jobinson99/EV-KuaFu/docs/images/mmexport1573315276697.jpg

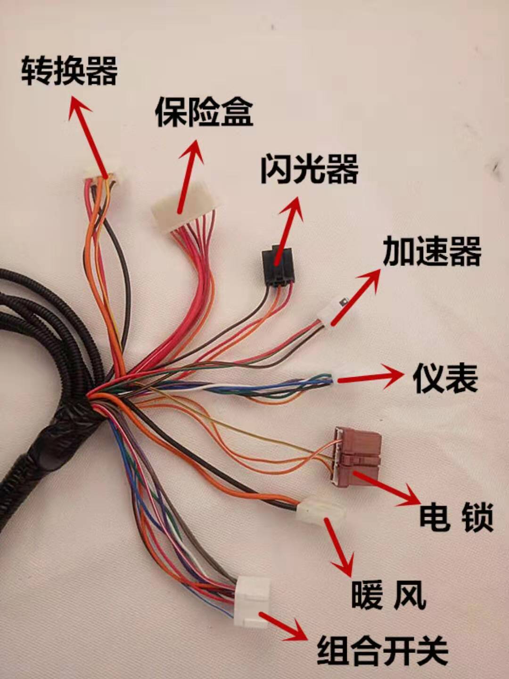
docs/images/mmexport1573315276697.jpg
