jobinson99/EV-KuaFu/docs/images/mmexport1573315287228.jpg

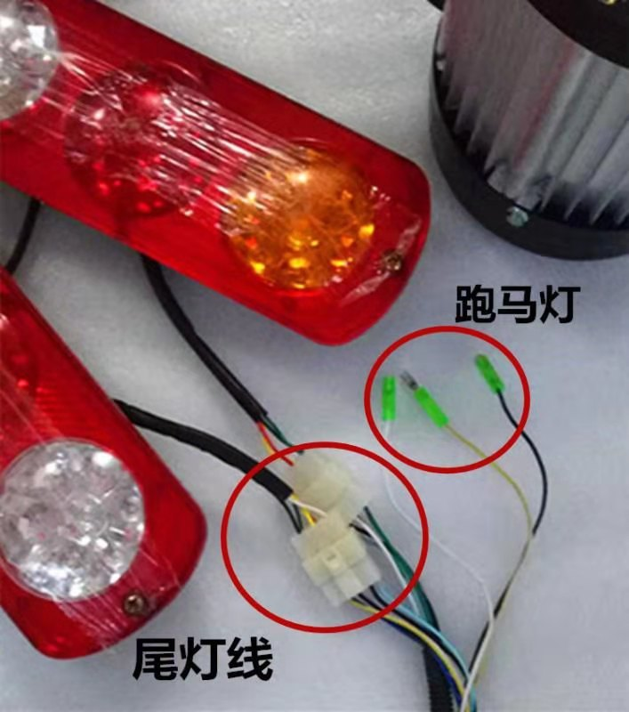
docs/images/mmexport1573315287228.jpg
