jobinson99/EV-KuaFu/docs/images/mmexport1573315331825.jpg

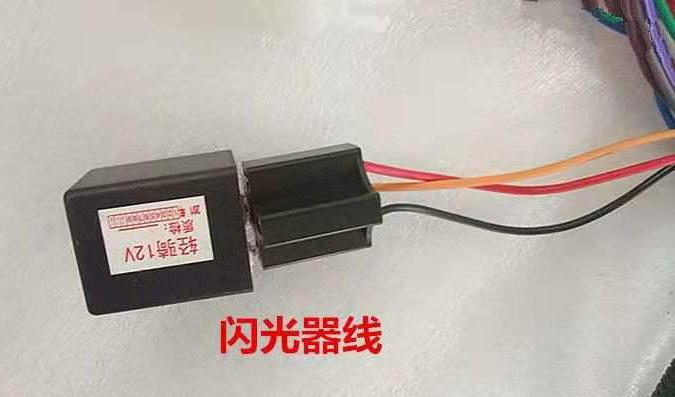
docs/images/mmexport1573315331825.jpg
