jobinson99/EV-KuaFu/docs/images/mmexport1573315335259.jpg

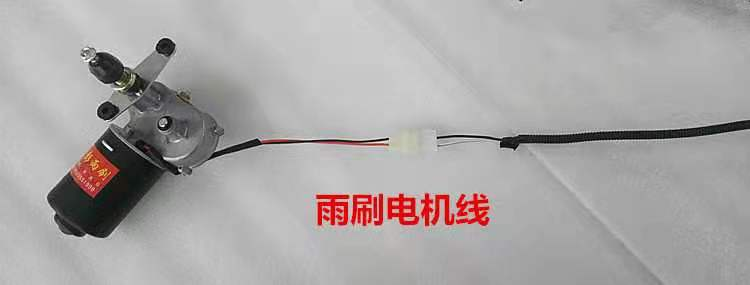
docs/images/mmexport1573315335259.jpg
