jobinson99/EV-KuaFu/docs/images/mmexport1573315338866.jpg

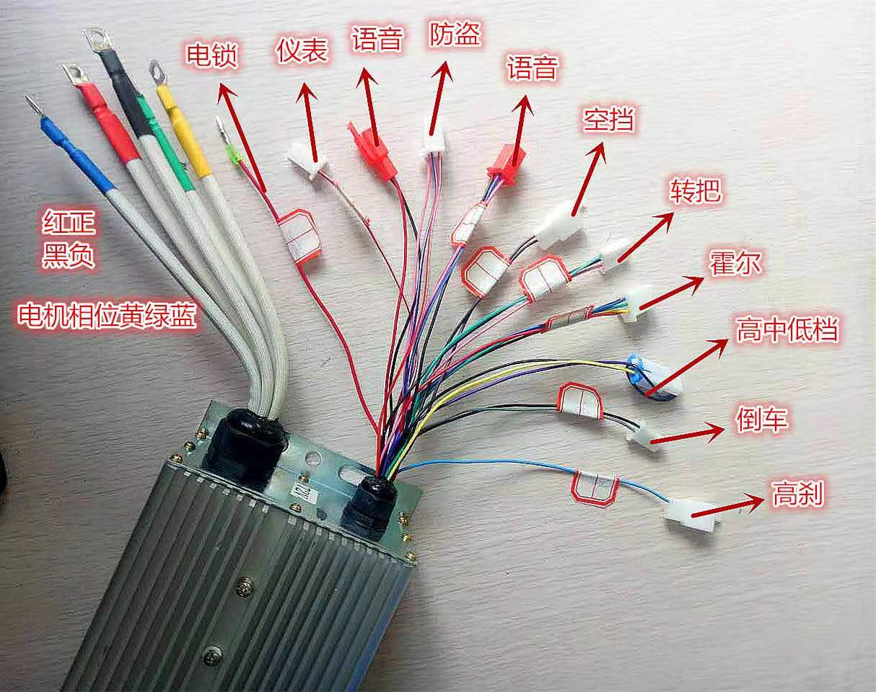
docs/images/mmexport1573315338866.jpg
