jobinson99/EV-KuaFu/docs/images/mmexport1573315342086.jpg

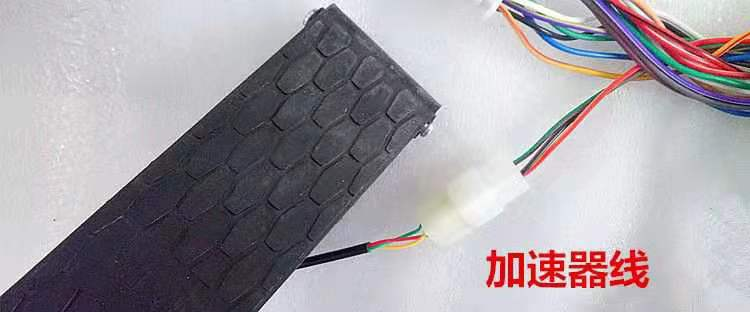
docs/images/mmexport1573315342086.jpg
