jobinson99/EV-KuaFu/docs/images/mmexport1573315346391.jpg

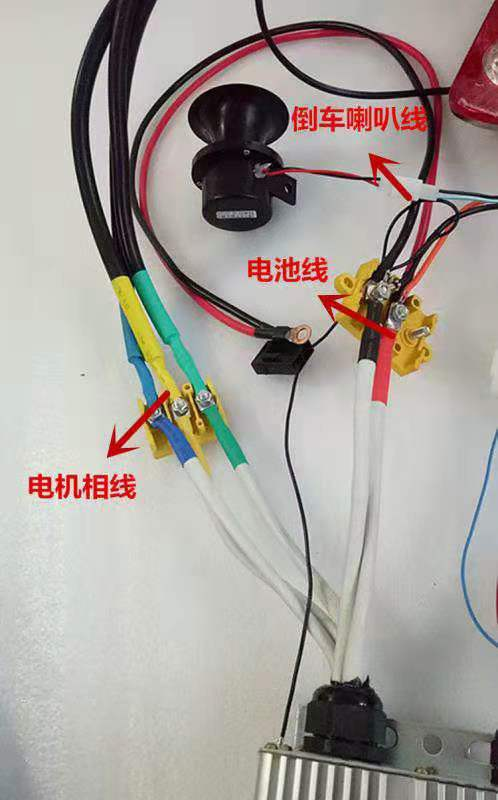
docs/images/mmexport1573315346391.jpg
