jobinson99/EV-KuaFu/docs/images/mmexport1573315385713.jpg

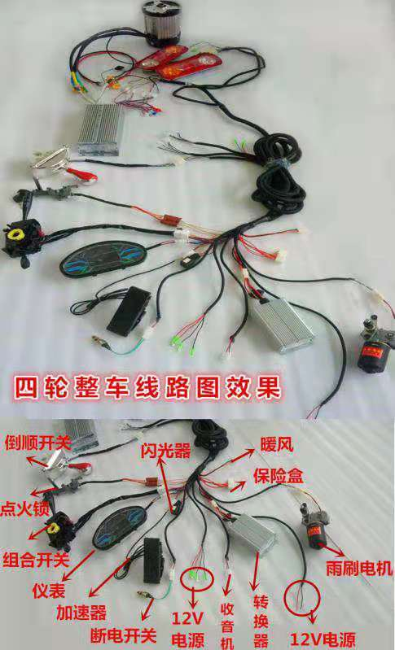
docs/images/mmexport1573315385713.jpg
