jobinson99/EV-KuaFu/docs/images/mmexport1573315388638.jpg

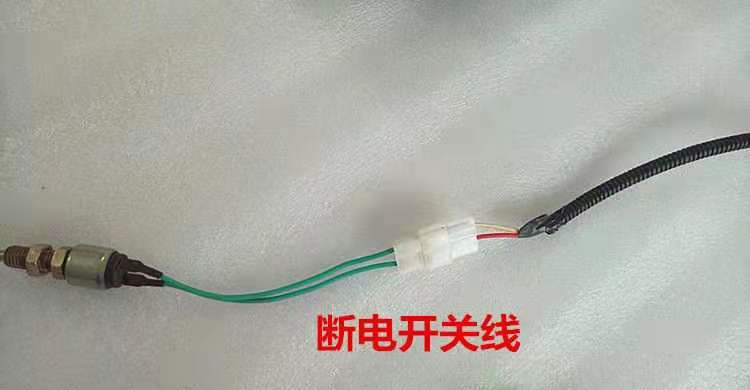
docs/images/mmexport1573315388638.jpg
