jobinson99/EV-KuaFu/docs/images/mmexport1573315394884.jpg

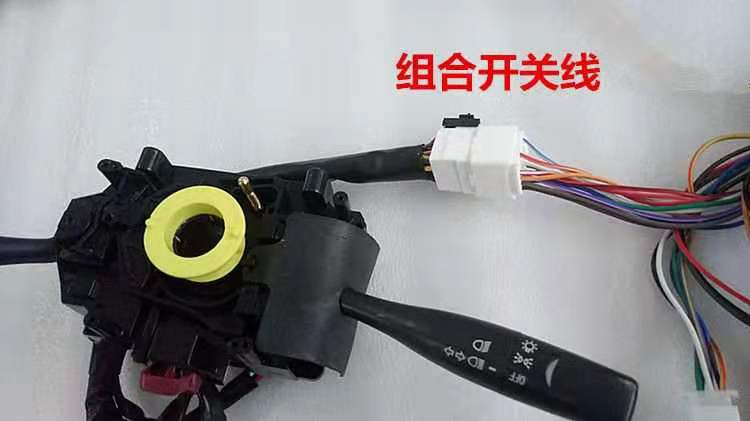
docs/images/mmexport1573315394884.jpg
