jobinson99/EV-KuaFu/docs/images/mmexport1574041762110.jpg

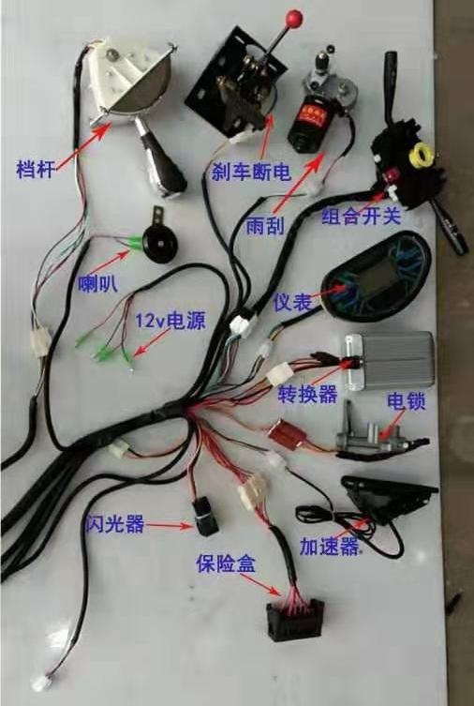
docs/images/mmexport1574041762110.jpg
