jobinson99/EV-KuaFu/docs/images/mmexport1574041777564.jpg

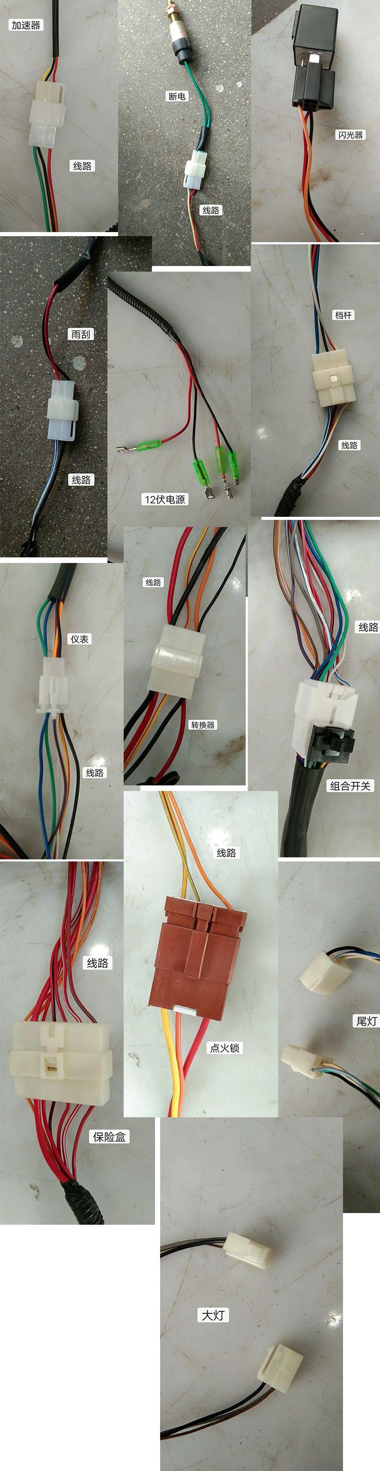
docs/images/mmexport1574041777564.jpg
