jobinson99/EV-KuaFu/docs/images/mmexport1574041887798.jpg

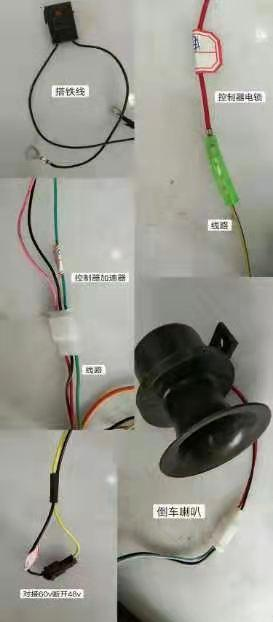
docs/images/mmexport1574041887798.jpg
