jobinson99/EV-KuaFu/docs/images/mmexport1574042124254.jpg

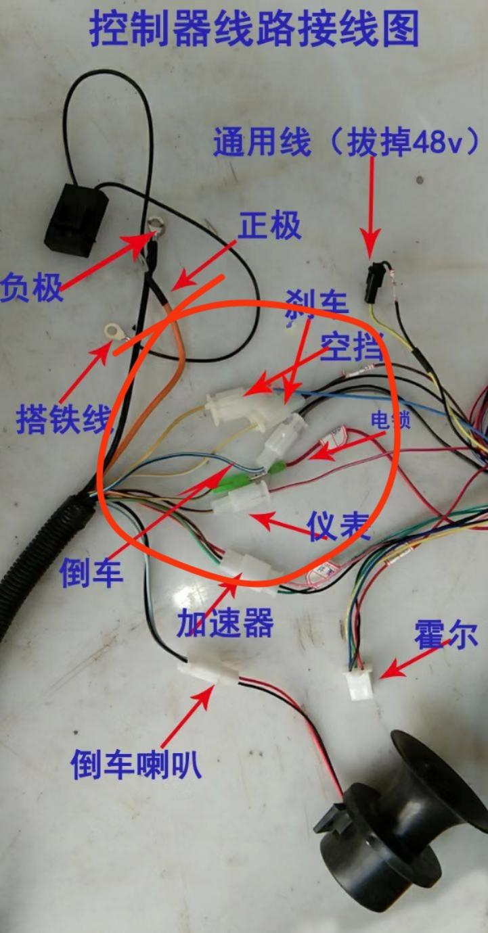
docs/images/mmexport1574042124254.jpg
