jobinson99/EV-KuaFu/docs/images/mmexport1574042128400.jpg

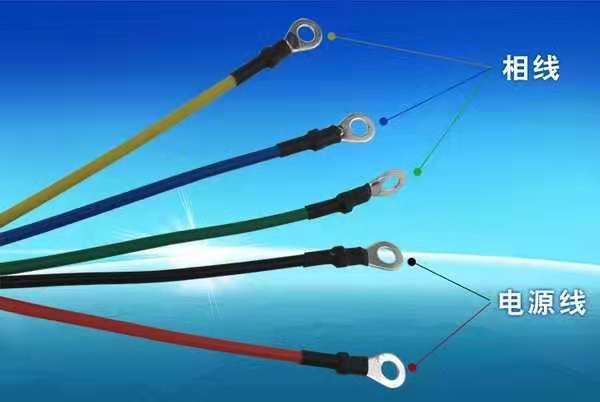
docs/images/mmexport1574042128400.jpg
