jobinson99/EV-KuaFu/docs/images/mmexport1574042167985.jpg

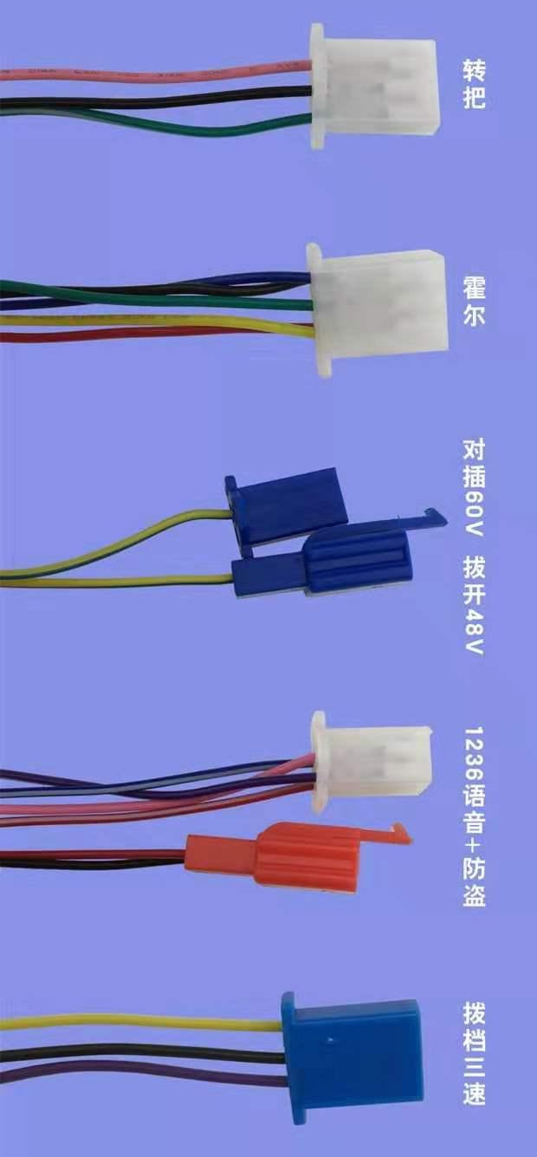
docs/images/mmexport1574042167985.jpg
